benmcmorran/rbe2001/CAD/zrarmsby_drive_space_3.stl

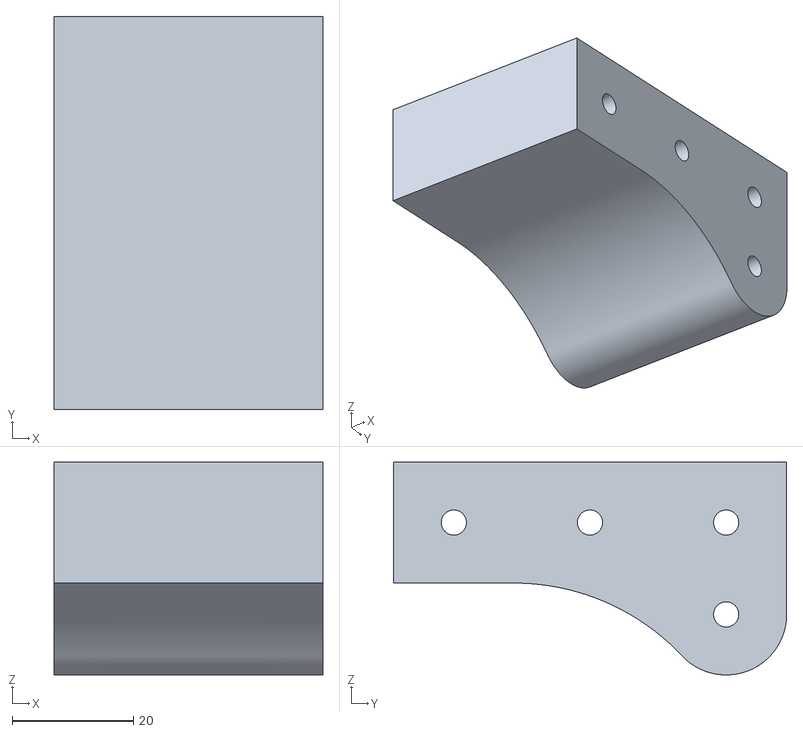
[picture p15: CAD file, 2016-03-01]
CAD/zrarmsby_drive_space_3.stl
44.5 x 65.0 x 35.2
