benmcmorran/rbe2001/CAD/zrarmsby_roller_insert_2001.stl

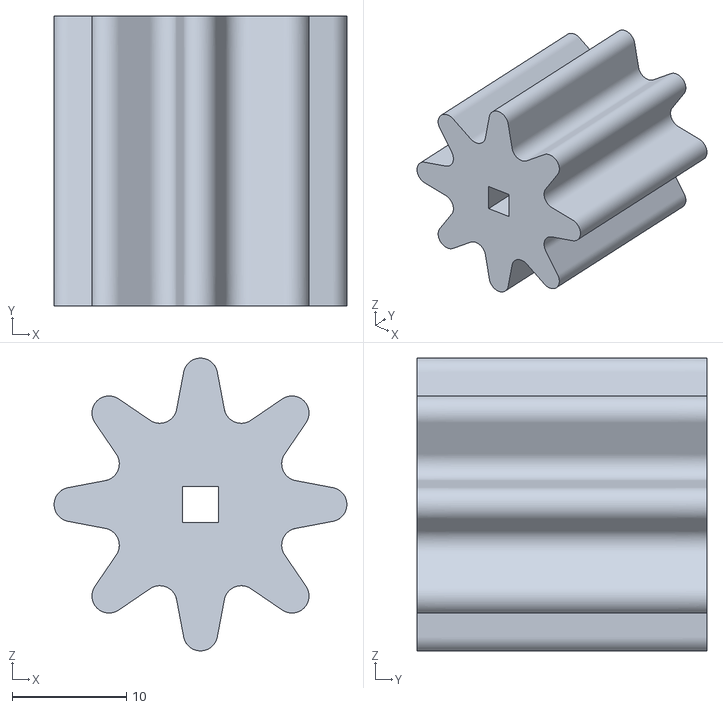
[picture p16: CAD file, 2016-03-01]
CAD/zrarmsby_roller_insert_2001.stl
25.6 x 25.4 x 25.6
