benmcmorran/rbe2001/CAD/zrarmsby_roller_2001_v2.stl

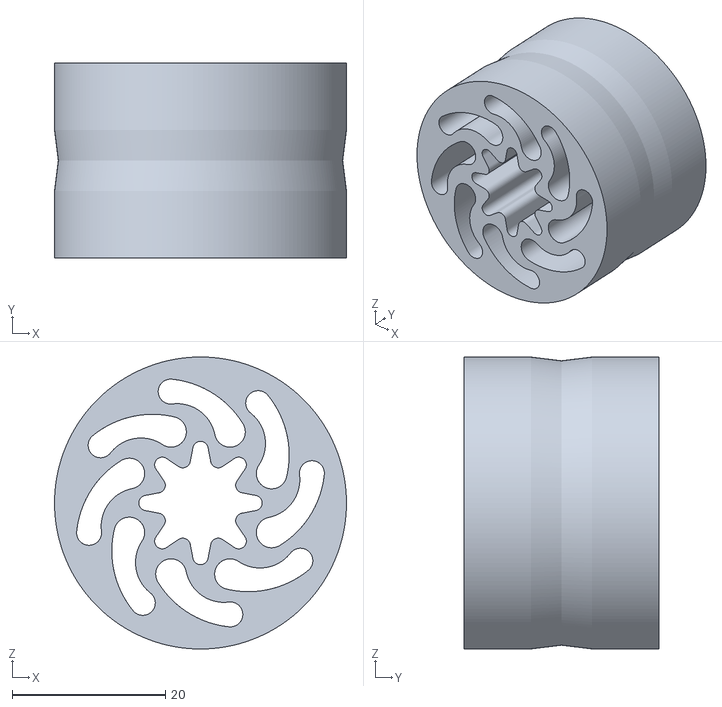
[picture p17: CAD file, 2016-03-01]
CAD/zrarmsby_roller_2001_v2.stl
38.1 x 25.4 x 38.1
