benmcmorran/rbe2001/CAD/top_plate.dxf

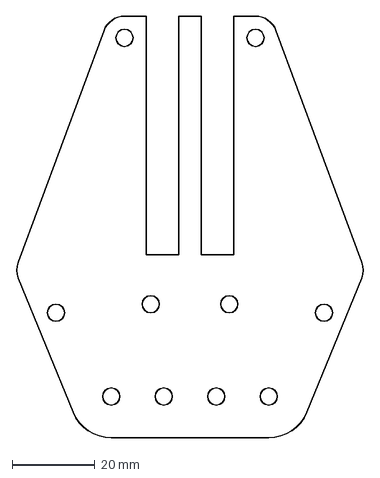
[picture p18: CAD file, 2016-03-01]
CAD/top_plate.dxf
84.1 x 102.1 mm
