benmcmorran/rbe2001/CAD/zrarmsby_rsl_mount.stl

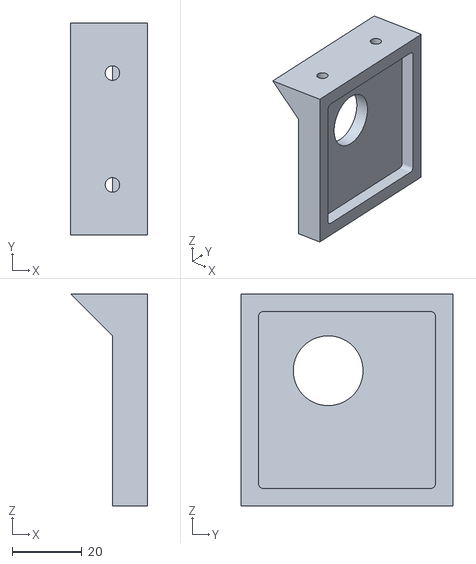
[picture p19: CAD file, 2016-03-01]
CAD/zrarmsby_rsl_mount.stl
22.0 x 60.8 x 60.8
