benmcmorran/rbe2001/CAD/zrarmsby_electonics_holder_spacer.stl

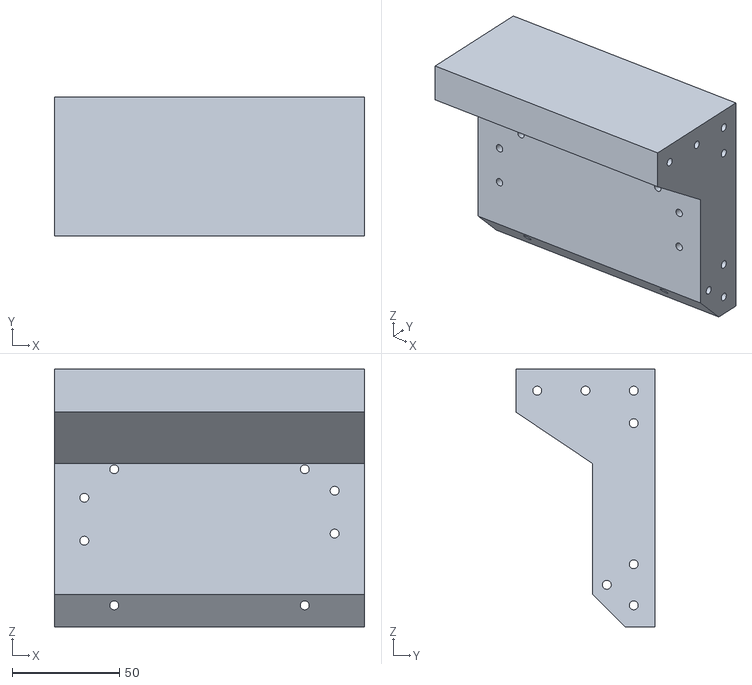
[picture p20: CAD file, 2016-03-01]
CAD/zrarmsby_electonics_holder_spacer.stl
144.6 x 65.0 x 120.2
