benmcmorran/rbe2001/CAD/zrarmsby_endstop_mirror.stl

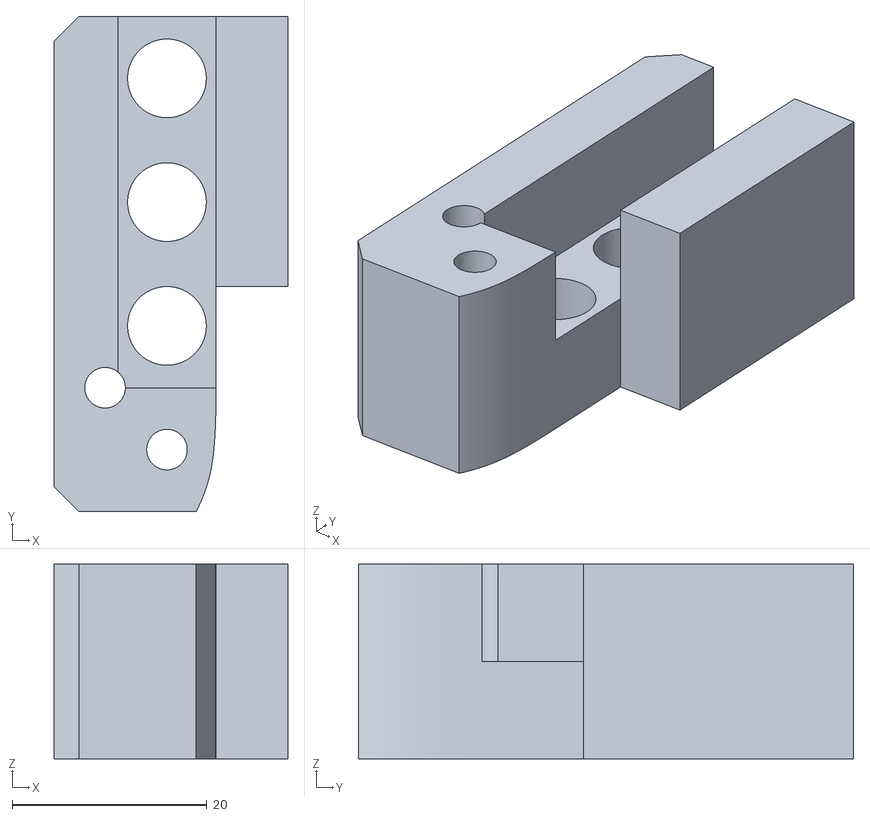
[picture p21: CAD file, 2016-03-01]
CAD/zrarmsby_endstop_mirror.stl
24.0 x 50.8 x 20.0
