benmcmorran/rbe2001/team12_robot/song_tone.cpp

#include "Arduino.h"
#include "pitches.h"

// Code from http://www.instructables.com/id/Aruino-Tone-RTTL-Player


#define OCTAVE_OFFSET 0

int notes[] = { 0,
NOTE_C4, NOTE_CS4, NOTE_D4, NOTE_DS4, NOTE_E4, NOTE_F4, NOTE_FS4, NOTE_G4, NOTE_GS4, NOTE_A4, NOTE_AS4, NOTE_B4,
NOTE_C5, NOTE_CS5, NOTE_D5, NOTE_DS5, NOTE_E5, NOTE_F5, NOTE_FS5, NOTE_G5, NOTE_GS5, NOTE_A5, NOTE_AS5, NOTE_B5,
NOTE_C6, NOTE_CS6, NOTE_D6, NOTE_DS6, NOTE_E6, NOTE_F6, NOTE_FS6, NOTE_G6, NOTE_GS6, NOTE_A6, NOTE_AS6, NOTE_B6,
NOTE_C7, NOTE_CS7, NOTE_D7, NOTE_DS7, NOTE_E7, NOTE_F7, NOTE_FS7, NOTE_G7, NOTE_GS7, NOTE_A7, NOTE_AS7, NOTE_B7
};

//char *song = "The Simpsons:d=4,o=5,b=160:c.6,e6,f#6,8a6,g.6,e6,c6,8a,8f#,8f#,8f#,2g,8p,8p,8f#,8f#,8f#,8g,a#.,8c6,8c6,8c6,c6";
//char *song = "TakeOnMe:d=4,o=4,b=160:8f#5,8f#5,8f#5,8d5,8p,8b,8p,8e5,8p,8e5,8p,8e5,8g#5,8g#5,8a5,8b5,8a5,8a5,8a5,8e5,8p,8d5,8p,8f#5,8p,8f#5,8p,8f#5,8e5,8e5,8f#5,8e5,8f#5,8f#5,8f#5,8d5,8p,8b,8p,8e5,8p,8e5,8p,8e5,8g#5,8g#5,8a5,8b5,8a5,8a5,8a5,8e5,8p,8d5,8p,8f#5,8p,8f#5,8p,8f#5,8e5,8e5";
//char *song = "Entertainer:d=4,o=5,b=140:8d,8d#,8e,c6,8e,c6,8e,2c.6,8c6,8d6,8d#6,8e6,8c6,8d6,e6,8b,d6,2c6,p,8d,8d#,8e,c6,8e,c6,8e,2c.6,8p,8a,8g,8f#,8a,8c6,e6,8d6,8c6,8a,2d6";
//char *song = "Muppets:d=4,o=5,b=250:c6,c6,a,b,8a,b,g,p,c6,c6,a,8b,8a,8p,g.,p,e,e,g,f,8e,f,8c6,8c,8d,e,8e,8e,8p,8e,g,2p,c6,c6,a,b,8a,b,g,p,c6,c6,a,8b,a,g.,p,e,e,g,f,8e,f,8c6,8c,8d,e,8e,d,8d,c";
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
//char *song = "smbdeath:d=4,o=5,b=90:32c6,32c6,32c6,8p,16b,16f6,16p,16f6,16f.6,16e.6,16d6,16c6,16p,16e,16p,16c";
//char *song = "ducktales:d=4,o=5,b=112:8e6,8e6,16p,16g6,8b6,g#6,p,8e6,8d6,8c6,8d6,8e6,8d6,8c6,8d6,8e6,8e6,16p,16g6,8b6,g#6,p,8e6,8d6,8c6,8d6,8e6,8d6,8c6,8g6,8e6,8e6";
//char *song = "Zelda1:d=4,o=5,b=125:a#,f.,8a#,16a#,16c6,16d6,16d#6,2f6,8p,8f6,16f.6,16f#6,16g#.6,2a#.6,16a#.6,16g#6,16f#.6,8g#.6,16f#.6,2f6,f6,8d#6,16d#6,16f6,2f#6,8f6,8d#6,8c#6,16c#6,16d#6,2f6,8d#6,8c#6,8c6,16c6,16d6,2e6,g6,8f6,16f,16f,8f,16f,16f,8f,16f,16f,8f,8f,a#,f.,8a#,16a#,16c6,16d6,16d#6,2f6,8p,8f6,16f.6,16f#6,16g#.6,2a#.6,c#7,c7,2a6,f6,2f#.6,a#6,a6,2f6,f6,2f#.6,a#6,a6,2f6,d6,2d#.6,f#6,f6,2c#6,a#,c6,16d6,2e6,g6,8f6,16f,16f,8f,16f,16f,8f,16f,16f,8f,8f";
//char *song = "smario2:d=4,o=5,b=125:8g,16c,8e,8g.,16c,8e,16g,16c,16e,16g,8b,a,8p,16c,8g,16c,8e,8g.,16c,8e,16g,16c#,16e,16g,8b,a,8p,16b,8c6,16b,8c6,8a.,16c6,8b,16a,8g,16f#,8g,8e.,16c,8d,16e,8f,16e,8f,8b.4,16e,8d.,c";
//char *song = "smb3lvl1:d=4,o=5,b=80:16g,32c,16g.,16a,32c,16a.,16b,32c,16b,16a.,32g#,16a.,16g,32c,16g.,16a,32c,16a,4b.,32p,16c6,32f,16c.6,16d6,32f,16d.6,16e6,32f,16e6,16d.6,32c#6,16d.6,16c6,32f,16c.6,16d6,32f,16d6,4e.6,32p,16g,32c,16g.,16a,32c,16a.,16b,32c,16b,16a.,32g#,16a.,16c6,8c.6,32p,16c6,4c.6";
//char *song = "shinobi:d=4,o=5,b=140:b,f#6,d6,b,g,f#,e,2f#.,a,1f#,p,b,f#6,d6,b,g,f#,e,1f#.,8a,1b.,8a,1f#.,8a,1b.,8a,1f#.";
//char *song = "outrun_magic:d=4,o=5,b=160:f6,d#6,8g#.6,f6,d#6,8c#.6,d#6,c6,2g#.,c#6,c6,8d#.6,c#6,c6,8f.,a#,16c.6,1a#,f6,d#6,8g#.6,f6,d#6,8c#.6,d#6,c6,2g#.,c#6,c6,8d#.6,c#6,c6,16f.,16g#.,c6,2a#.";
//char *song = "Popeye:d=4,o=5,b=140:16g.,16f.,16g.,16p,32p,16c.,16p,32p,16c.,16p,32p,16e.,16d.,16c.,16d.,16e.,16f.,g,8p,16a,16f,16a,16c6,16b,16a,16g,16a,16g,8e,16g,16g,16g,16g,8a,16b,32c6,32b,32c6,32b,32c6,32b,8c6";
//char *song = "Wonderboy:d=4,o=5,b=225:f6,d6,f6,8d6,f6,32p,8f6,d6,f6,d6,e6,c6,e6,8c6,e6,32p,8e6,c6,e6,c6";
//char *song = "smwwd1:d=4,o=5,b=125:a,8f.,16c,16d,16f,16p,f,16d,16c,16p,16f,16p,16f,16p,8c6,8a.,g,16c,a,8f.,16c,16d,16f,16p,f,16d,16c,16p,16f,16p,16a#,16a,16g,2f,16p,8a.,8f.,8c,8a.,f,16g#,16f,16c,16p,8g#.,2g,8a.,8f.,8c,8a.,f,16g#,16f,8c,2c6";
//char *song = "dkong:d=4,o=5,b=160:2c,8d.,d#.,c.,16b,16c6,16b,16c6,16b,16c6,16b,16c6,16b,16c6,16b,16c6,16b,2c6";
//char *song = "dkong:d=4,o=5,b=160:2c,8d.,d#.,c.,16b,16c6,16b,16c6,16b,16c6,16b,16c6,16b,16c6,16b,16c6,16b,2c6";

#define isdigit(n) (n >= '0' && n <= '9')

void play_rtttl(char *p)
{
  // Absolutely no error checking in here

  byte default_dur = 4;
  byte default_oct = 6;
  int bpm = 63;
  int num;
  long wholenote;
  long duration;
  byte note;
  byte scale;

  // format: d=N,o=N,b=NNN:
  // find the start (skip name, etc)

  while(*p != ':') p++;    // ignore name
  p++;                     // skip ':'

  // get default duration
  if(*p == 'd')
  {
    p++; p++;              // skip "d="
    num = 0;
    while(isdigit(*p))
    {
      num = (num * 10) + (*p++ - '0');
    }
    if(num > 0) default_dur = num;
    p++;                   // skip comma
  }

  //Serial.print("ddur: "); Serial.println(default_dur, 10);

  // get default octave
  if(*p == 'o')
  {
    p++; p++;              // skip "o="
    num = *p++ - '0';
    if(num >= 3 && num <=7) default_oct = num;
    p++;                   // skip comma
  }

  //Serial.print("doct: "); Serial.println(default_oct, 10);

  // get BPM
  if(*p == 'b')
  {
    p++; p++;              // skip "b="
    num = 0;
    while(isdigit(*p))
    {
      num = (num * 10) + (*p++ - '0');
    }
    bpm = num;
    p++;                   // skip colon
  }

  //Serial.print("bpm: "); Serial.println(bpm, 10);

  // BPM usually expresses the number of quarter notes per minute
  wholenote = (60 * 1000L / bpm) * 4;  // this is the time for whole note (in milliseconds)

  //Serial.print("wn: "); Serial.println(wholenote, 10);


  // now begin note loop
  while(*p)
  {
    // first, get note duration, if available
    num = 0;
    while(isdigit(*p))
    {
      num = (num * 10) + (*p++ - '0');
    }
   
    if(num) duration = wholenote / num;
    else duration = wholenote / default_dur;  // we will need to check if we are a dotted note after

    // now get the note
    note = 0;

    switch(*p)
    {
      case 'c':
        note = 1;
        break;
      case 'd':
        note = 3;
        break;
      case 'e':
        note = 5;
        break;
      case 'f':
        note = 6;
        break;
      case 'g':
        note = 8;
        break;
      case 'a':
        note = 10;
        break;
      case 'b':
        note = 12;
        break;
      case 'p':
      default:
        note = 0;
    }
    p++;

    // now, get optional '#' sharp
    if(*p == '#')
    {
      note++;
      p++;
    }

    // now, get optional '.' dotted note
    if(*p == '.')
    {
      duration += duration/2;
      p++;
    }
 
    // now, get scale
    if(isdigit(*p))
    {
      scale = *p - '0';
      p++;
    }
    else
    {
      scale = default_oct;
    }

    scale += OCTAVE_OFFSET;

    if(*p == ',')
      p++;       // skip comma for next note (or we may be at the end)

    // now play the note

    if(note)
    {
      //Serial.print("Playing: ");
      //Serial.print(scale, 10); Serial.print(' ');
      //Serial.print(note, 10); Serial.print(" (");
      //Serial.print(notes[(scale - 4) * 12 + note], 10);
      //Serial.print(") ");
      //Serial.println(duration, 10);
      tone(12,notes[(scale - 4) * 12 + note],duration);
      delay(duration);
      noTone(12);
    }
    else
    {
      //Serial.print("Pausing: ");
      //Serial.println(duration, 10);
      delay(duration);
    }
  }
}
