benmcmorran/rbe2001/team12_robot/song_tone.h

#ifndef TONE_H
#define TONE_H

// Code from biomech75 at http://www.instructables.com/id/Aruino-Tone-RTTL-Player

char *song = "Indiana:d=4,o=5,b=250:e,8p,8f,8g,8p,1c6,8p.,d,8p,8e,1f,p.,g,8p,8a,8b,8p,1f6,p,a,8p,8b,2c6,2d6,2e6,e,8p,8f,8g,8p,1c6,p,d6,8p,8e6,1f.6,g,8p,8g,e.6,8p,d6,8p,8g,e.6,8p,d6,8p,8g,f.6,8p,e6,8p,8d6,2c6";
void play_rtttl(char *p);

#endif
